nbremond77/Autoduino-v4/Hardware/rev 4/Output/Images/Autoduino-rev4 - A.png

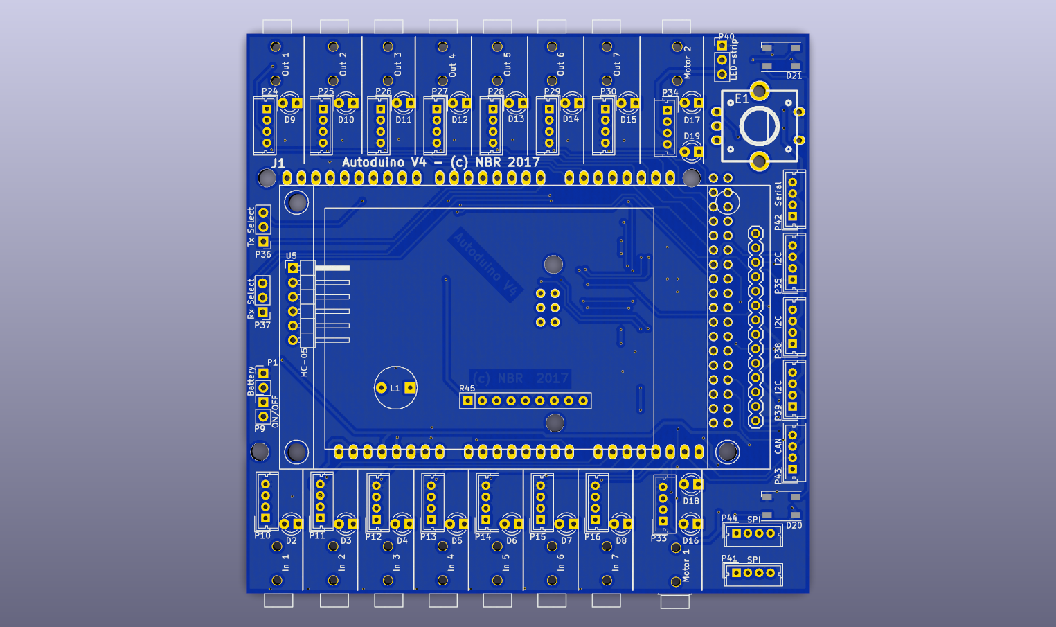
Hardware/rev 4/Output/Images/Autoduino-rev4 - A.png
