nbremond77/Autoduino-v4/Hardware/rev 4/Output/Images/Autoduino-rev4 - B.png

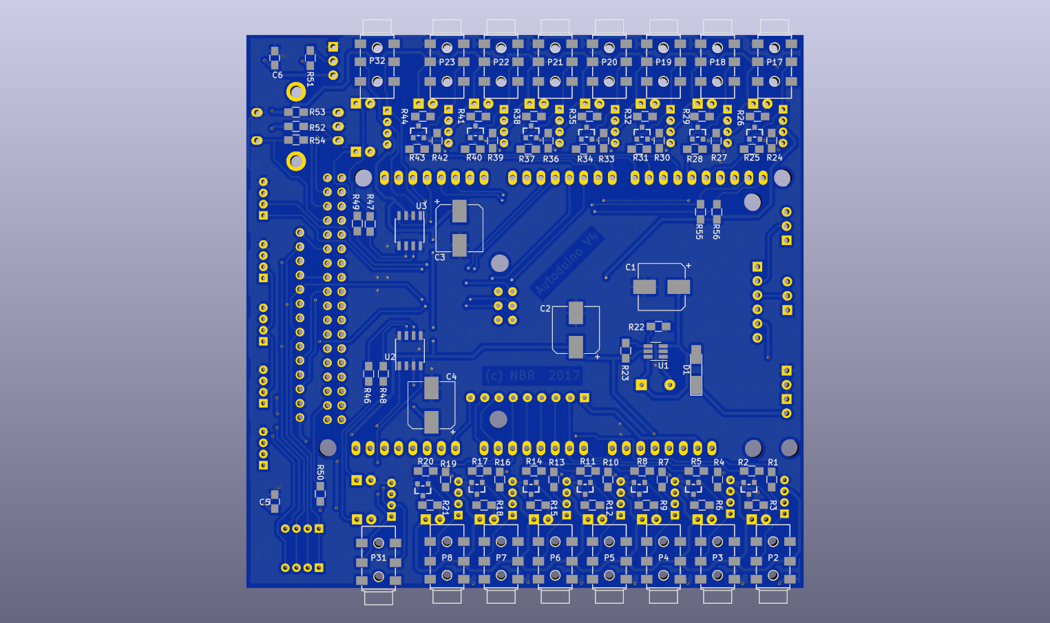
Hardware/rev 4/Output/Images/Autoduino-rev4 - B.png
