nbremond77/Autoduino-v4/Hardware/rev 4/Output/Autoduino-rev4.pdf

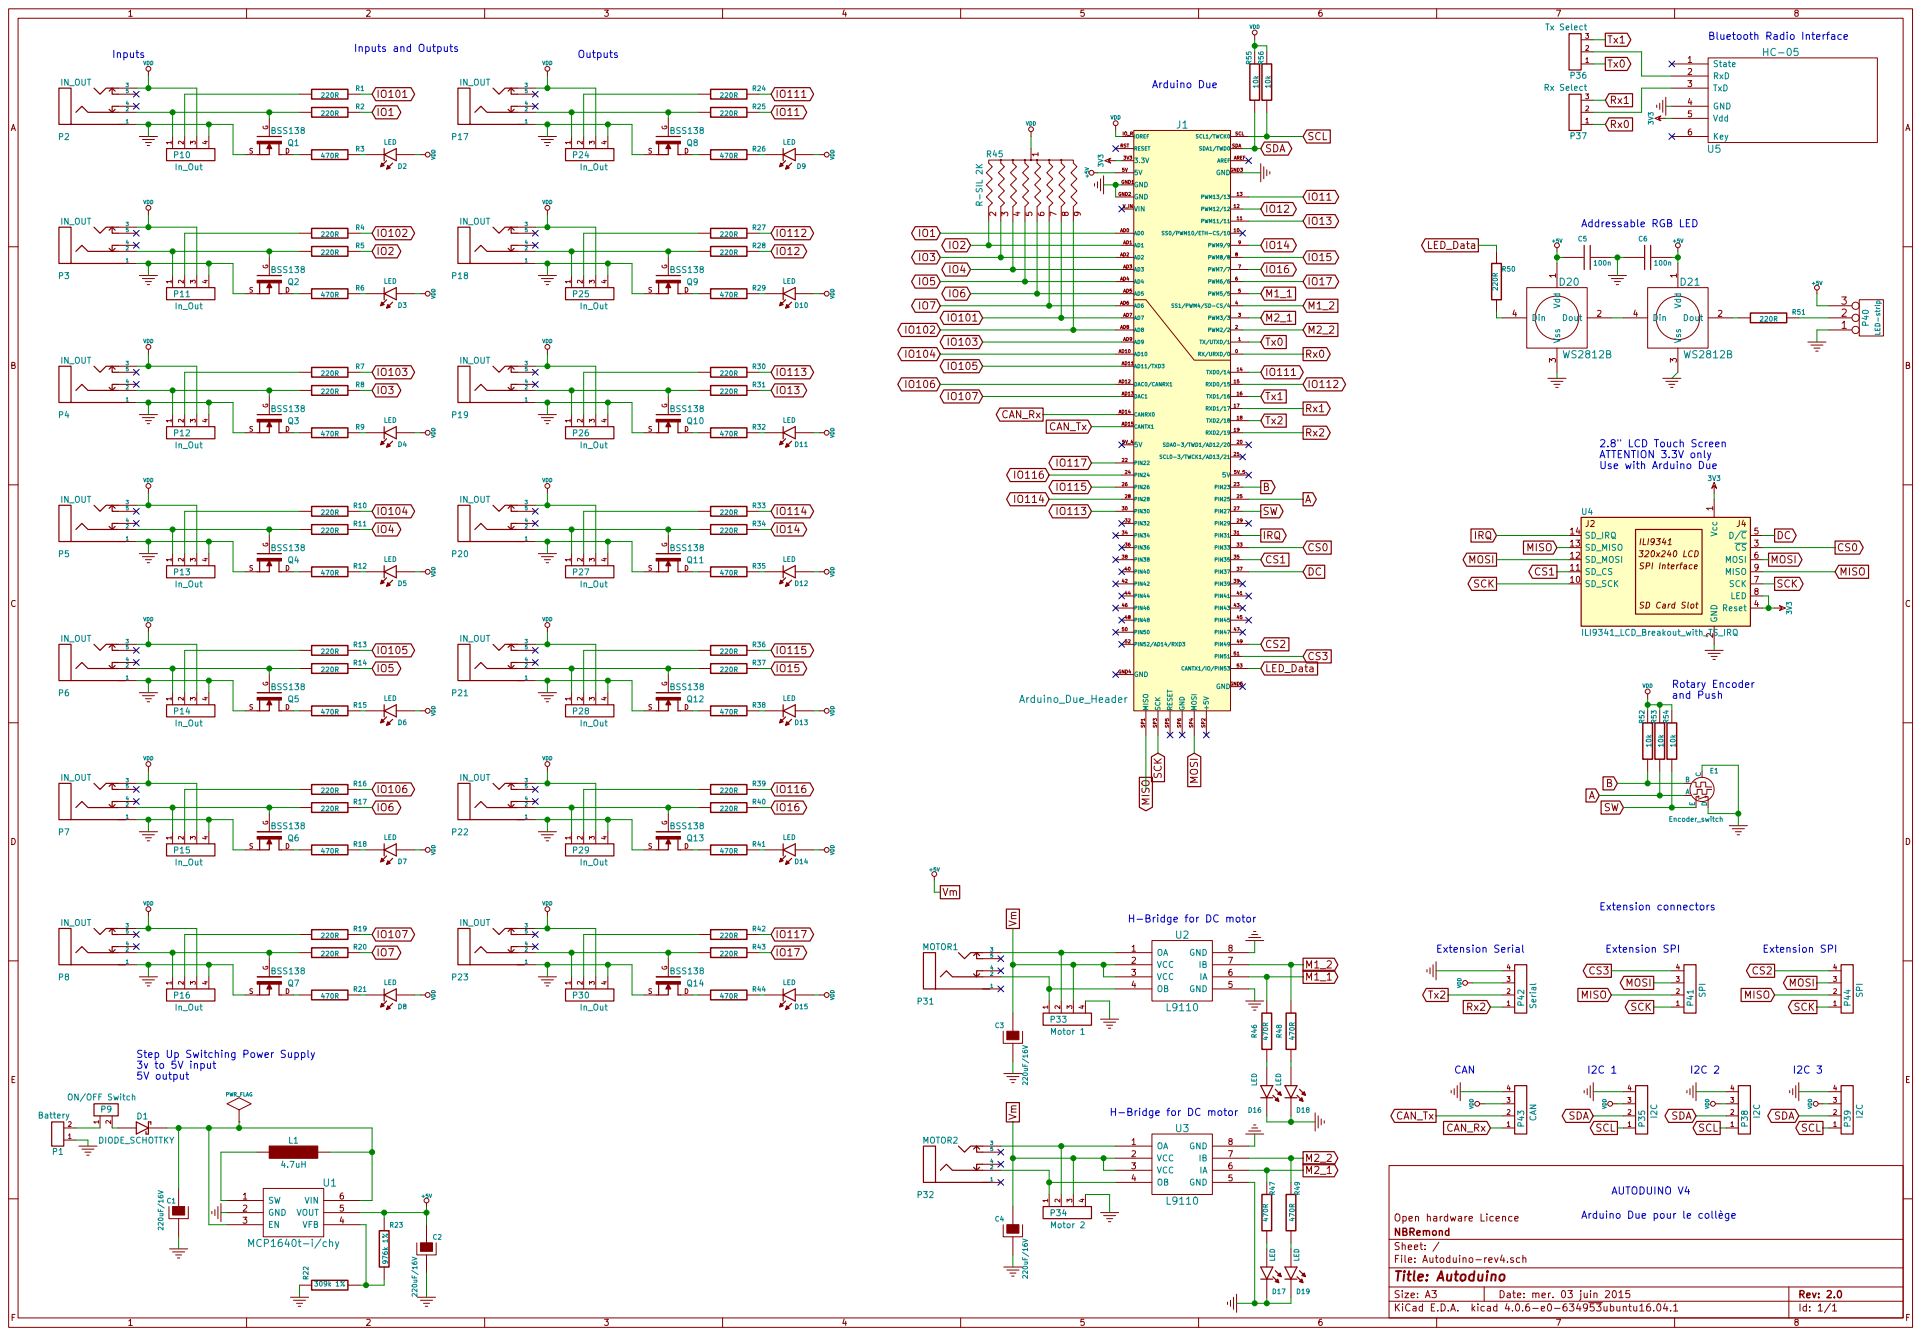
[picture p5: page 1]

ATTENTION 3.3V only Use with Arduino Due Vm

Rotary Encoder and Push Extension connectors SCL

+5V Step Up Switching Power Supply

H-Bridge for DC motor

Arduino Due pour le collège 12 P1 Battery
