nbremond77/Autoduino-v4/Hardware/rev 4/Output/Autoduino-rev4-F.Fab.pdf

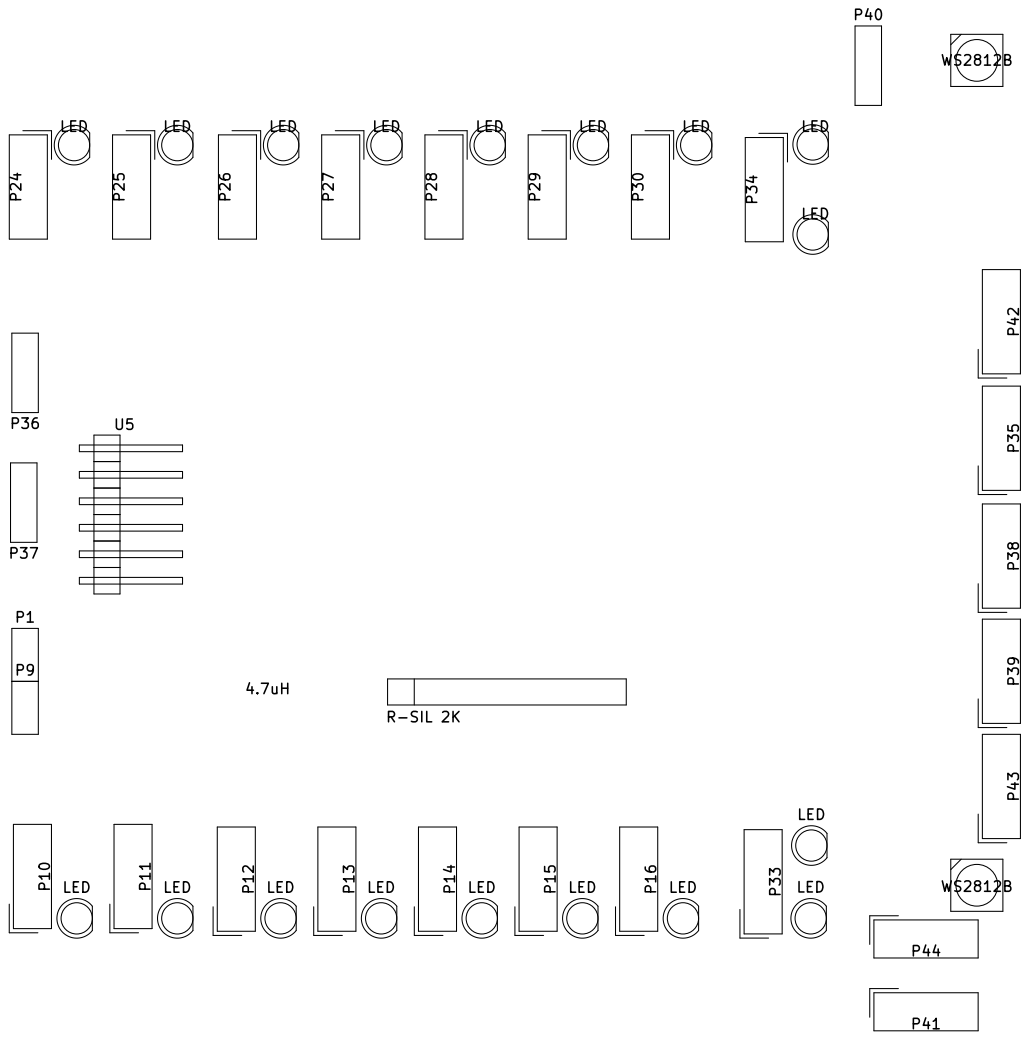
[picture p14: page 1]
