nbremond77/Autoduino-v4/Hardware/rev 4/Output/Autoduino-rev4-F.Mask.pdf

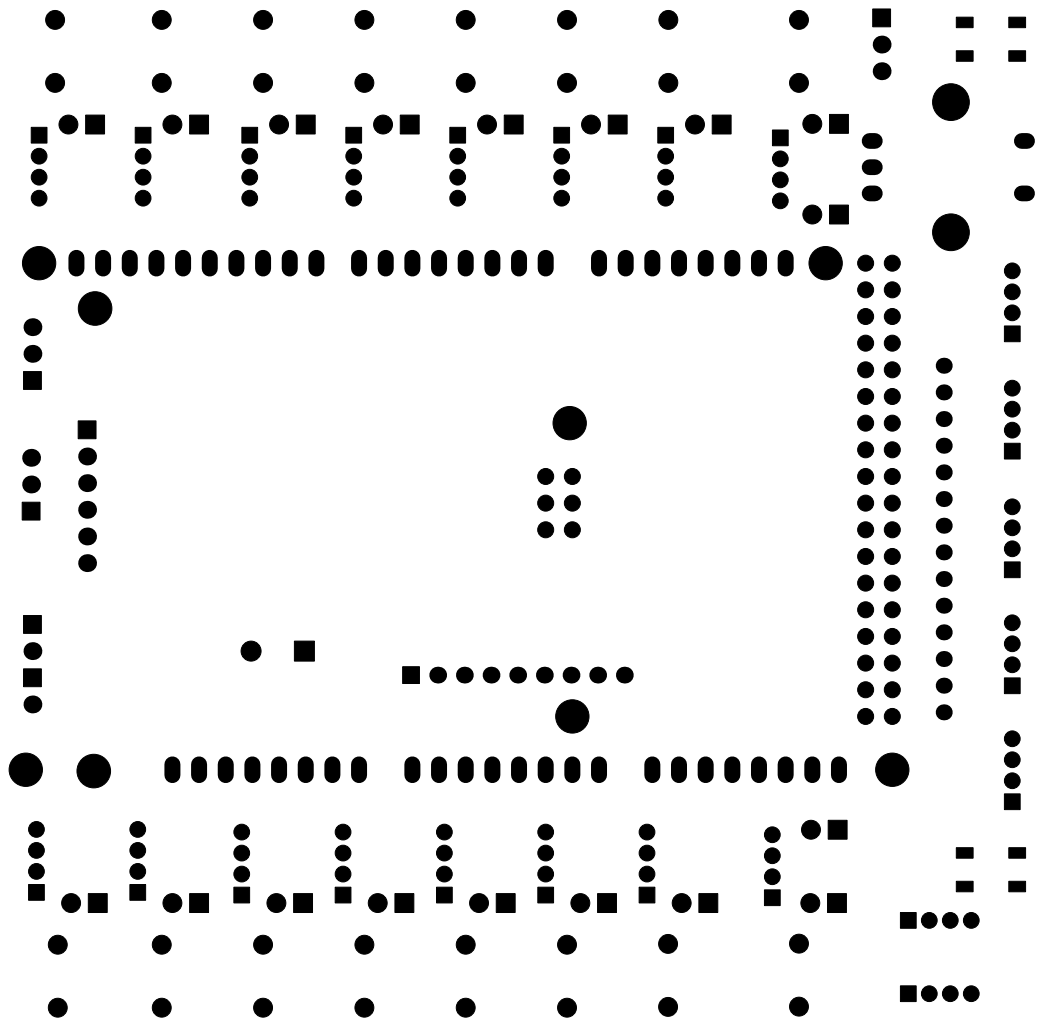
[picture p15: page 1]
