nbremond77/Autoduino-v4/Hardware/rev 4/Output/Autoduino-rev4-F.SilkS.pdf

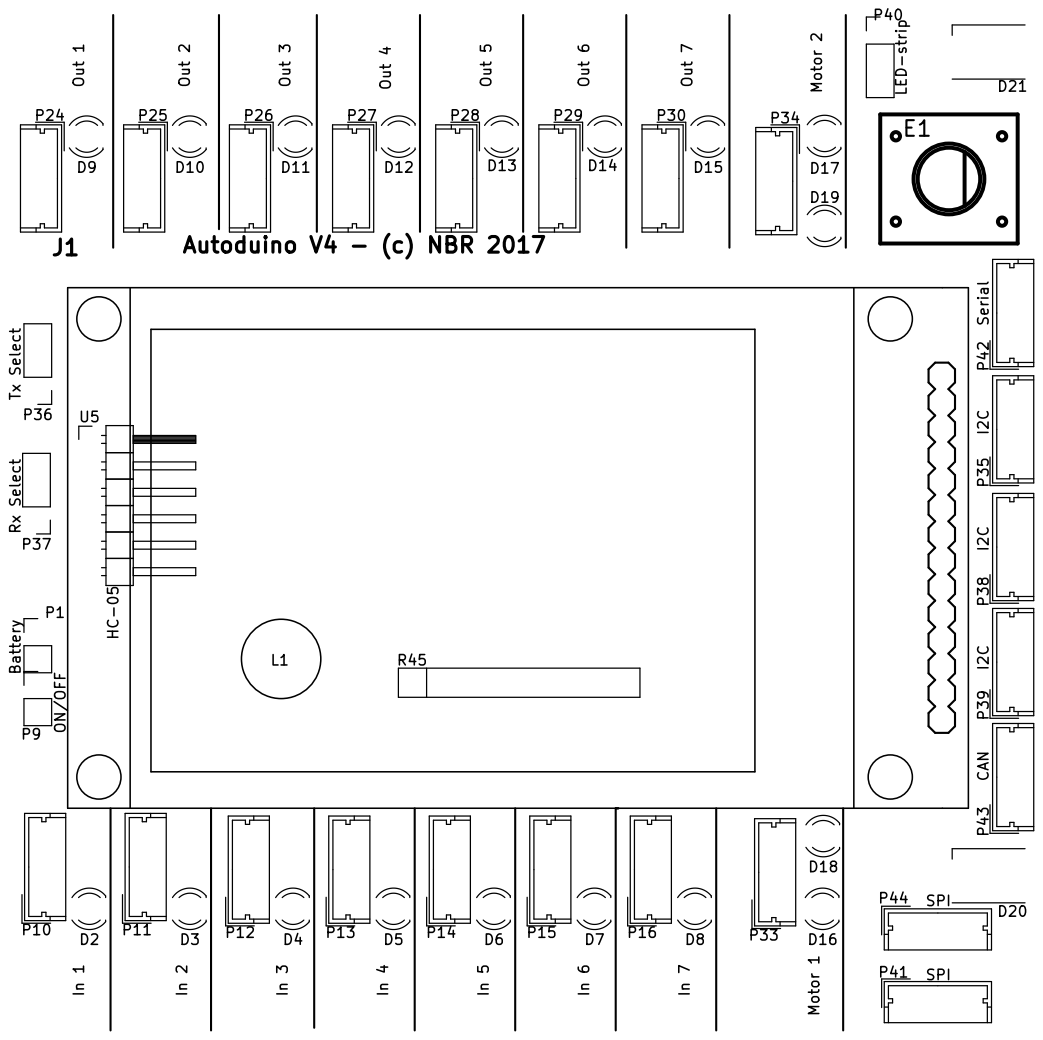
[picture p16: page 1]
